Andrew-Arcade/Andrew-Arcade/gamepad/pin-mappings.png

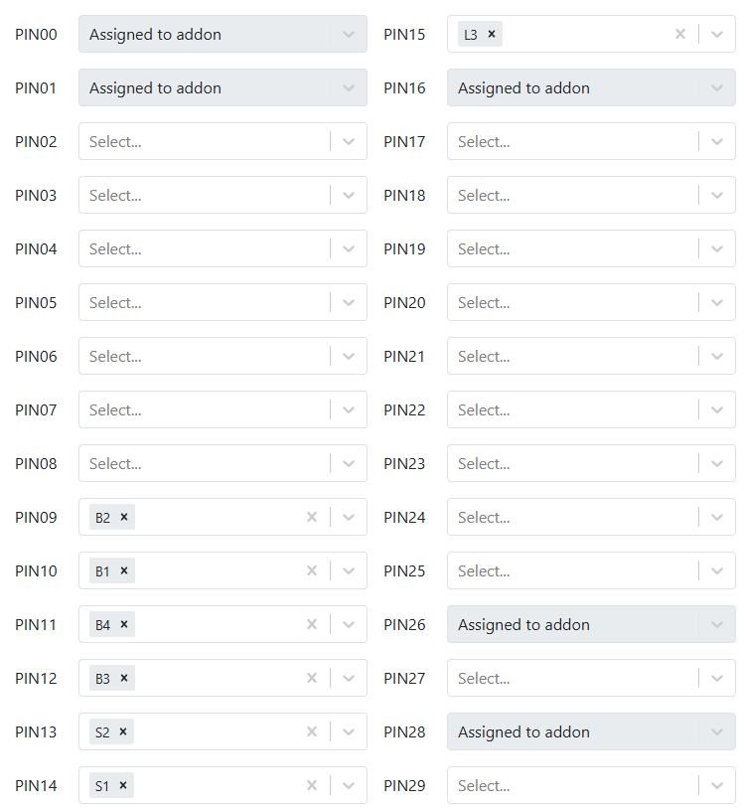
gamepad/pin-mappings.png
