Andrew-Arcade/Andrew-Arcade/gamepad/waveshare-2040-zero-pinout.png

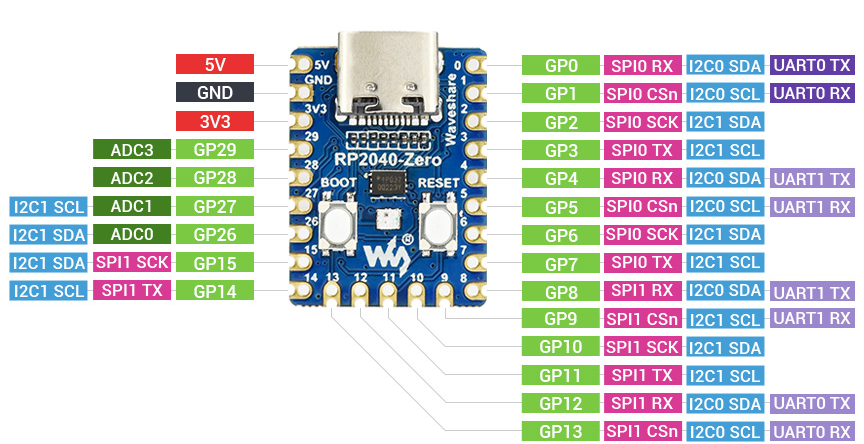
gamepad/waveshare-2040-zero-pinout.png
